sladorsoft/Intel8088OnBreadboard/schematics/part04/part04_1.kicad_sch

## KiCad design schematics/part04/part04_1.kicad_sch (2022-03-15)

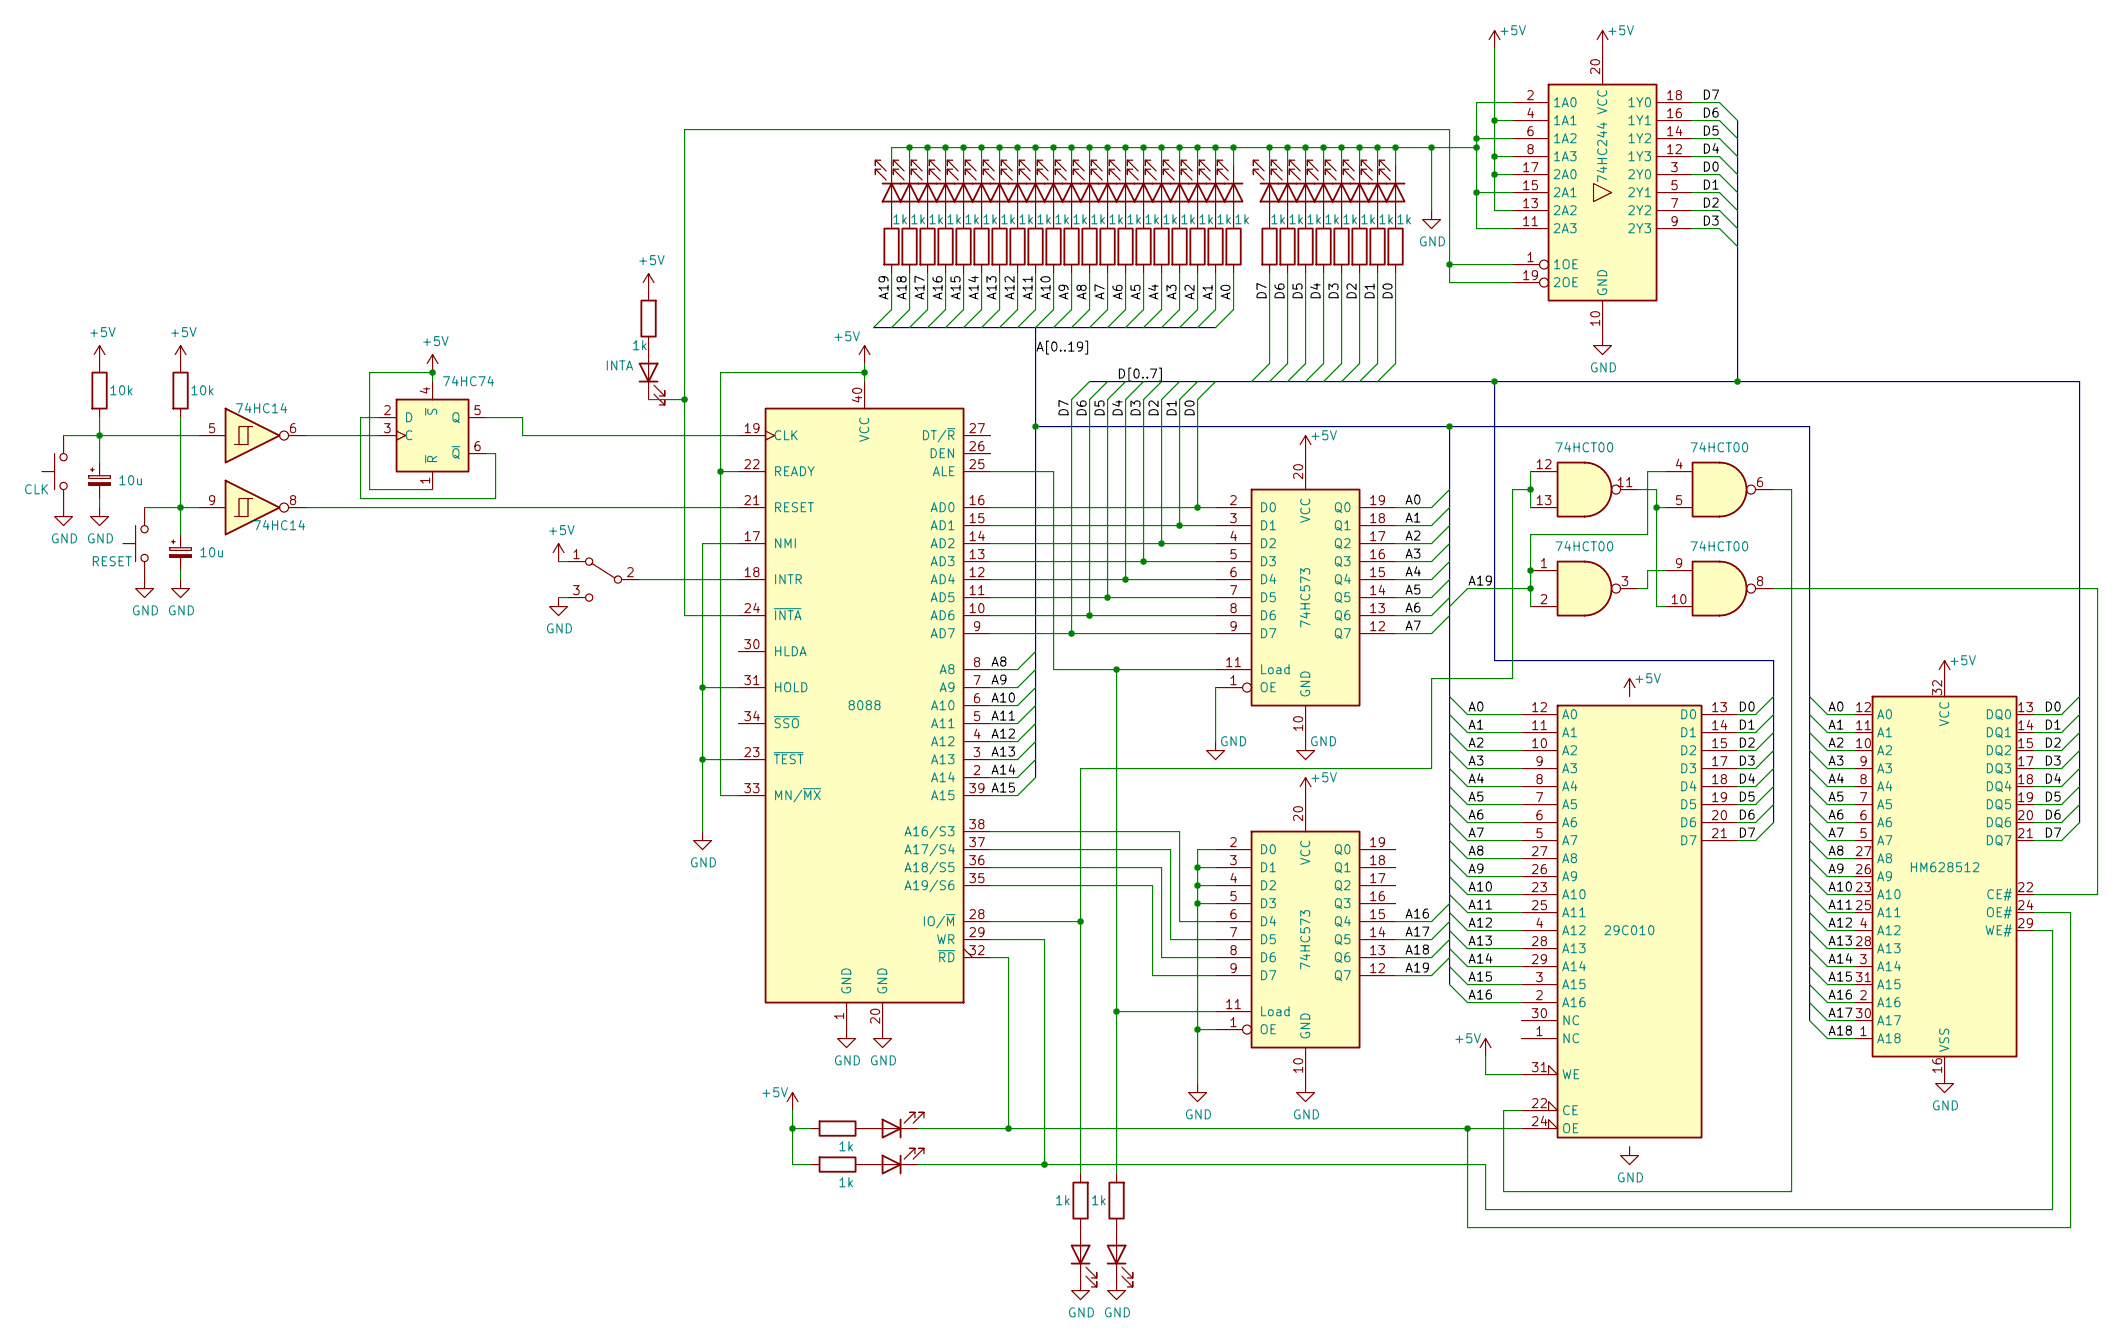
[picture p13: schematic part04_1.kicad_sch]

Parts:
SW1: INT
U1: 8088; DIP-40_W15.24mm
U2, U3: 74HC573
U4: 29C010
U5: 74HCT00
U6: HM628512; DIP-32_W15.24mm
U7: 74HC244
U101: 74HC74
U102: 74HC14

Connections:
+5V: U1.22 (READY), U1.33 (MN/~MX), U1.40 (VCC), U2.20 (VCC), U3.20 (VCC), U4.32 (VCC), U101.1 (~R), U101.4 (~S)
A0: U2.19 (Q0), U4.12 (A0), U6.12 (A0)
A1: U2.18 (Q1), U4.11 (A1), U6.11 (A1)
A2: U2.17 (Q2), U4.10 (A2), U6.10 (A2)
A3: U2.16 (Q3), U4.9 (A3), U6.9 (A3)
A4: U2.15 (Q4), U4.8 (A4), U6.8 (A4)
A5: U2.14 (Q5), U4.7 (A5), U6.7 (A5)
A6: U2.13 (Q6), U4.6 (A6), U6.6 (A6)
A7: U2.12 (Q7), U4.5 (A7), U6.5 (A7)
A8: U1.8 (A8), U4.27 (A8), U6.27 (A8)
A9: U1.7 (A9), U4.26 (A9), U6.26 (A9)
A10: U1.6 (A10), U4.23 (A10), U6.23 (A10)
A11: U1.5 (A11), U4.25 (A11), U6.25 (A11)
A12: U1.4 (A12), U4.4 (A12), U6.4 (A12)
A13: U1.3 (A13), U4.28 (A13), U6.28 (A13)
A14: U1.2 (A14), U4.29 (A14), U6.3 (A14)
A15: U1.39 (A15), U4.3 (A15), U6.31 (A15)
A16: U3.15 (Q4), U4.2 (A16), U6.2 (A16)
A17: U3.14 (Q5), U6.30 (A17)
A18: U3.13 (Q6), U6.1 (A18)
A19: U3.12 (Q7), U5.1, U5.2, U5.4
D0: U1.16 (AD0), U2.2 (D0), U4.13 (D0), U6.13 (DQ0), U7.3 (2Y0)
D1: U1.15 (AD1), U2.3 (D1), U4.14 (D1), U6.14 (DQ1), U7.5 (2Y1)
D2: U1.14 (AD2), U2.4 (D2), U4.15 (D2), U6.15 (DQ2), U7.7 (2Y2)
D3: U1.13 (AD3), U2.5 (D3), U4.17 (D3), U6.17 (DQ3), U7.9 (2Y3)
D4: U1.12 (AD4), U2.6 (D4), U4.18 (D4), U6.18 (DQ4), U7.12 (1Y3)
D5: U1.11 (AD5), U2.7 (D5), U4.19 (D5), U6.19 (DQ5), U7.14 (1Y2)
D6: U1.10 (AD6), U2.8 (D6), U4.20 (D6), U6.20 (DQ6), U7.16 (1Y1)
D7: U1.9 (AD7), U2.9 (D7), U4.21 (D7), U6.21 (DQ7), U7.18 (1Y0)
GND: U1.1 (GND), U1.17 (NMI), U1.20 (GND), U1.23 (~TEST), U1.31 (HOLD), U2.1 (OE), U2.10 (GND), U3.1 (OE), U3.2 (D0), U3.3 (D1), U3.4 (D2), U3.5 (D3), U3.10 (GND), U4.16 (GND), U7.2 (1A0), U7.6 (1A2), U7.11 (2A3), U7.15 (2A1)
unnamed: SW1.2 (B), U1.18 (INTR)
unnamed: U1.19 (CLK), U101.5 (Q)
unnamed: U1.21 (RESET), U102.8
unnamed: U1.24 (~INTA), U7.1 (1OE), U7.19 (2OE)
unnamed: U1.25 (ALE), U2.11 (Load), U3.11 (Load)
unnamed: U1.28 (IO/~M), U5.12, U5.13
unnamed: U1.29 (WR), U6.29 (WE#)
unnamed: U1.32 (~RD), U4.24 (OE), U6.24 (OE#)
unnamed: U1.35 (A19/S6), U3.9 (D7)
unnamed: U1.36 (A18/S5), U3.8 (D6)
unnamed: U1.37 (A17/S4), U3.7 (D5)
unnamed: U1.38 (A16/S3), U3.6 (D4)
unnamed: U4.22 (CE), U5.6
unnamed: U5.3, U5.9
unnamed: U5.8, U6.22 (CE#)
unnamed: U5.5, U5.10, U5.11
unnamed: U7.4 (1A1), U7.8 (1A3), U7.13 (2A2), U7.17 (2A0)
unnamed: U101.2 (D), U101.6 (~Q)
unnamed: U101.3 (C), U102.6
