sladorsoft/Intel8088OnBreadboard/schematics/part06/part06_1.kicad_sch

## KiCad design schematics/part06/part06_1.kicad_sch (2022-04-28)

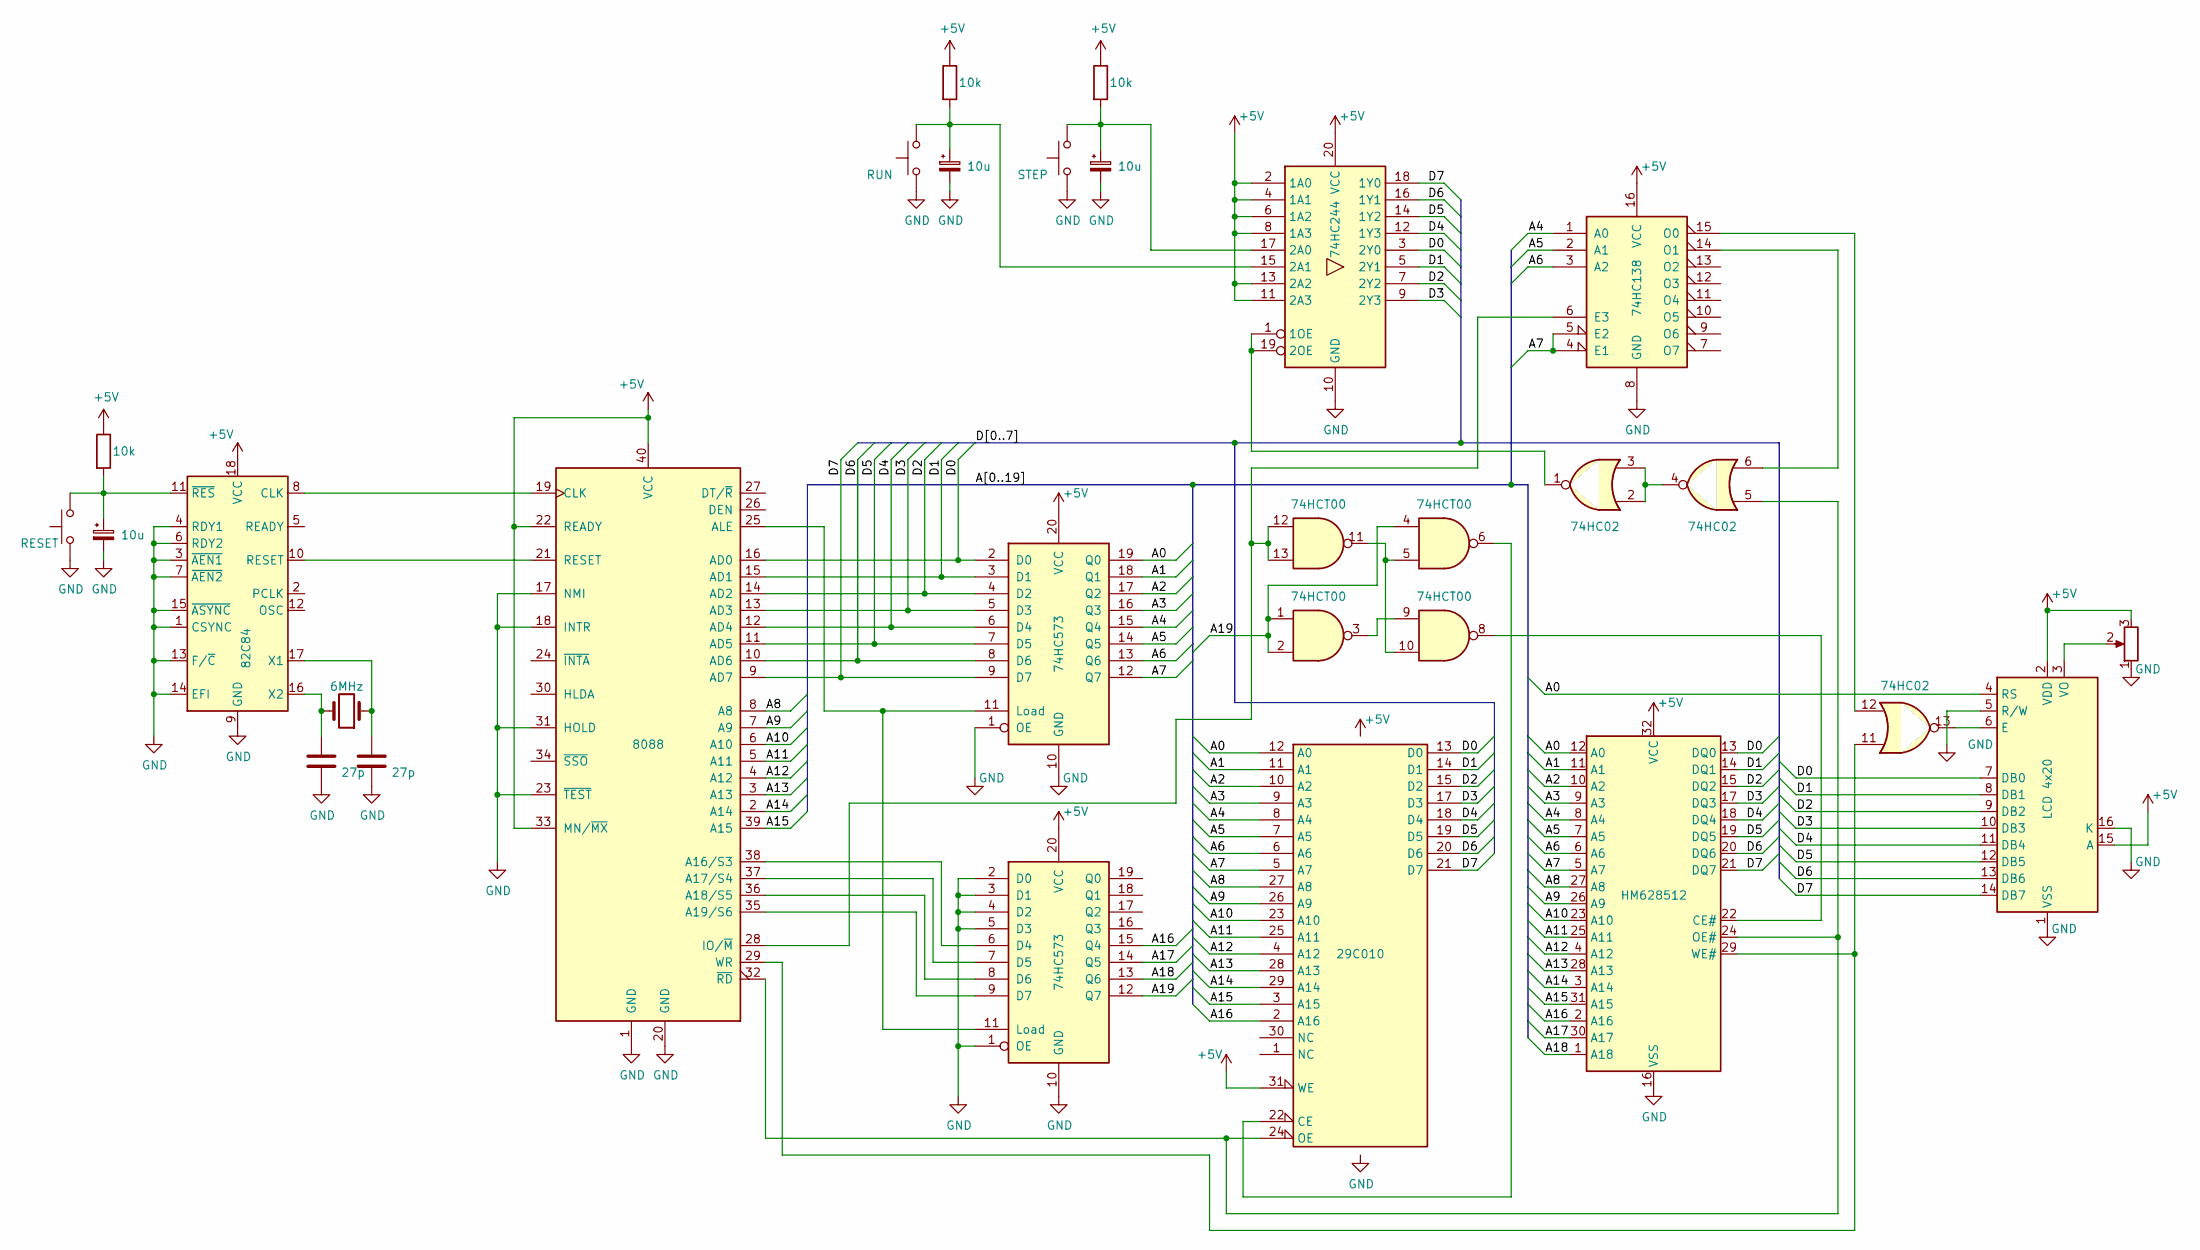
[picture p16: schematic part06_1.kicad_sch]

Parts:
C1, C4, C5: 10u
C2, C3: 27p
R1, R2, R3: 10k
RV1: R_Potentiometer
SW1: RESET
SW2: STEP
SW3: RUN
U1: 8088; DIP-40_W15.24mm
U2, U3: 74HC573
U4: 29C010
U5: 74HCT00
U6: HM628512; DIP-32_W15.24mm
U7: 74HC244
U8: 74HC138
U9: 74HC02
U10: LCD 4x20; NHD-0420H1Z
U11: 82C84; DIP-18_W7.62mm
Y1: 6MHz

Connections:
+5V: R1.1, R2.1, R3.1, RV1.3, U1.22 (READY), U1.33 (MN/~MX), U1.40 (VCC), U2.20 (VCC), U3.20 (VCC), U4.31 (PGM), U4.32 (VCC), U6.32 (VCC), U7.2 (1A0), U7.4 (1A1), U7.6 (1A2), U7.8 (1A3), U7.11 (2A3), U7.13 (2A2), U7.20 (VCC), U8.16 (VCC), U10.2 (VDD), U10.15 (A), U11.18 (VCC)
A0: U2.19 (Q0), U4.12 (A0), U6.12 (A0), U10.4 (RS)
A1: U2.18 (Q1), U4.11 (A1), U6.11 (A1)
A2: U2.17 (Q2), U4.10 (A2), U6.10 (A2)
A3: U2.16 (Q3), U4.9 (A3), U6.9 (A3)
A4: U2.15 (Q4), U4.8 (A4), U6.8 (A4), U8.1 (A0)
A5: U2.14 (Q5), U4.7 (A5), U6.7 (A5), U8.2 (A1)
A6: U2.13 (Q6), U4.6 (A6), U6.6 (A6), U8.3 (A2)
A7: U2.12 (Q7), U4.5 (A7), U6.5 (A7), U8.4 (E1), U8.5 (E2)
A8: U1.8 (A8), U4.27 (A8), U6.27 (A8)
A9: U1.7 (A9), U4.26 (A9), U6.26 (A9)
A10: U1.6 (A10), U4.23 (A10), U6.23 (A10)
A11: U1.5 (A11), U4.25 (A11), U6.25 (A11)
A12: U1.4 (A12), U4.4 (A12), U6.4 (A12)
A13: U1.3 (A13), U4.28 (A13), U6.28 (A13)
A14: U1.2 (A14), U4.29 (A14), U6.3 (A14)
A15: U1.39 (A15), U4.3 (A15), U6.31 (A15)
A16: U3.15 (Q4), U4.2 (A16), U6.2 (A16)
A17: U3.14 (Q5), U6.30 (A17)
A18: U3.13 (Q6), U6.1 (A18)
A19: U3.12 (Q7), U5.1, U5.2, U5.4
D0: U1.16 (AD0), U2.2 (D0), U4.13 (D0), U6.13 (DQ0), U7.3 (2Y0), U10.7 (DB0)
D1: U1.15 (AD1), U2.3 (D1), U4.14 (D1), U6.14 (DQ1), U7.5 (2Y1), U10.8 (DB1)
D2: U1.14 (AD2), U2.4 (D2), U4.15 (D2), U6.15 (DQ2), U7.7 (2Y2), U10.9 (DB2)
D3: U1.13 (AD3), U2.5 (D3), U4.17 (D3), U6.17 (DQ3), U7.9 (2Y3), U10.10 (DB3)
D4: U1.12 (AD4), U2.6 (D4), U4.18 (D4), U6.18 (DQ4), U7.12 (1Y3), U10.11 (DB4)
D5: U1.11 (AD5), U2.7 (D5), U4.19 (D5), U6.19 (DQ5), U7.14 (1Y2), U10.12 (DB5)
D6: U1.10 (AD6), U2.8 (D6), U4.20 (D6), U6.20 (DQ6), U7.16 (1Y1), U10.13 (DB6)
D7: U1.9 (AD7), U2.9 (D7), U4.21 (D7), U6.21 (DQ7), U7.18 (1Y0), U10.14 (DB7)
GND: C1.2, C2.2, C3.2, C4.2, C5.2, RV1.1, SW1.1, SW2.1, SW3.1, U1.1 (GND), U1.17 (NMI), U1.18 (INTR), U1.20 (GND), U1.23 (~TEST), U1.31 (HOLD), U2.1 (OE), U2.10 (GND), U3.1 (OE), U3.2 (D0), U3.3 (D1), U3.4 (D2), U3.5 (D3), U3.10 (GND), U4.16 (GND), U6.16 (VSS), U7.10 (GND), U8.8 (GND), U10.1 (VSS), U10.5 (R/W), U10.16 (K), U11.1 (CSYNC), U11.3 (~AEN1), U11.4 (RDY1), U11.6 (RDY2), U11.7 (~AEN2), U11.9 (GND), U11.13 (F/~C), U11.14 (EFI), U11.15 (~ASYNC)
unnamed: C1.1, R1.2, SW1.2, U11.11 (~RES)
unnamed: C2.1, U11.16 (X2), Y1.2
unnamed: C3.1, U11.17 (X1), Y1.1
unnamed: C4.1, R2.2, SW2.2, U7.17 (2A0)
unnamed: C5.1, R3.2, SW3.2, U7.15 (2A1)
unnamed: RV1.2, U10.3 (VO)
unnamed: U1.19 (CLK), U11.8 (CLK)
unnamed: U1.21 (RESET), U11.10 (RESET)
unnamed: U1.25 (ALE), U2.11 (Load), U3.11 (Load)
unnamed: U1.28 (IO/~M), U5.12, U5.13, U8.6 (E3)
unnamed: U1.29 (WR), U6.29 (WE#), U9.11
unnamed: U1.32 (~RD), U4.24 (OE), U6.24 (OE#), U9.5
unnamed: U1.35 (A19/S6), U3.9 (D7)
unnamed: U1.36 (A18/S5), U3.8 (D6)
unnamed: U1.37 (A17/S4), U3.7 (D5)
unnamed: U1.38 (A16/S3), U3.6 (D4)
unnamed: U4.22 (CE), U5.6
unnamed: U5.3, U5.9
unnamed: U5.8, U6.22 (CE#)
unnamed: U5.5, U5.10, U5.11
unnamed: U7.1 (1OE), U7.19 (2OE), U9.1
unnamed: U8.14 (O1), U9.6
unnamed: U8.15 (O0), U9.12
unnamed: U9.2, U9.3, U9.4
unnamed: U9.13, U10.6 (E)
