sladorsoft/Intel8088OnBreadboard/schematics/part08/part08.kicad_sch

## KiCad design schematics/part08/part08.kicad_sch (2023-01-09)

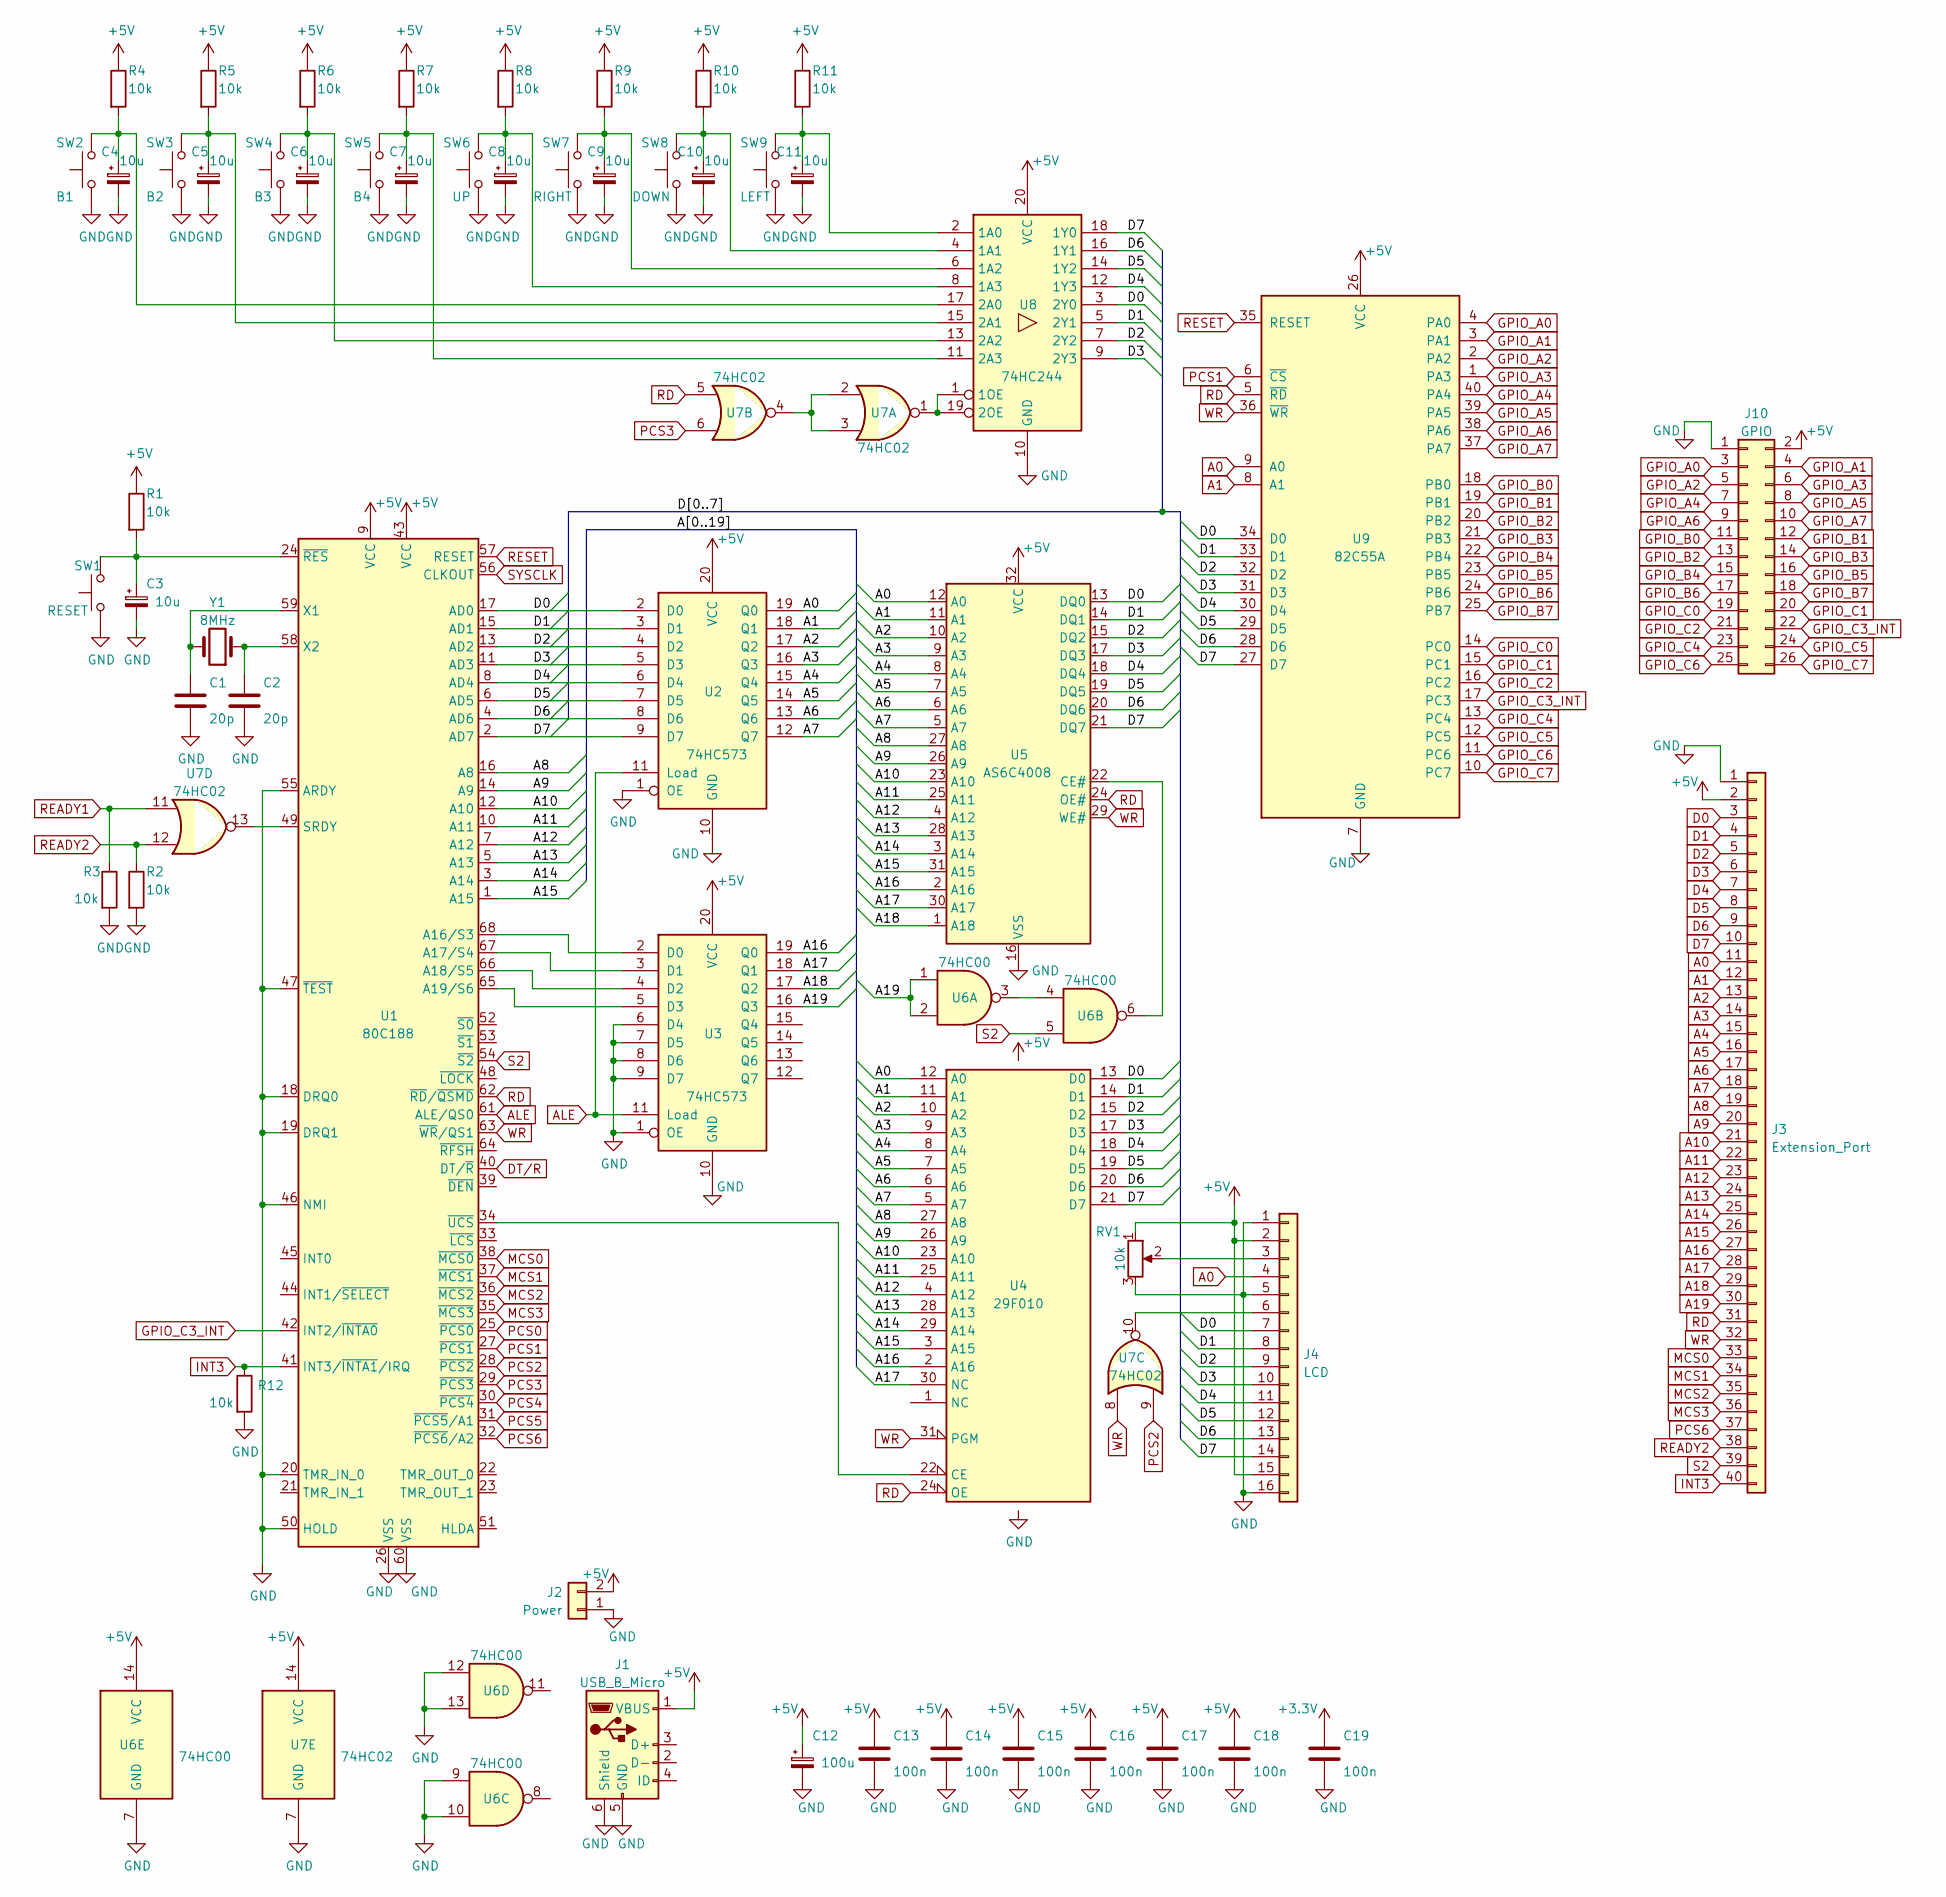
[picture p18: schematic part08.kicad_sch]

Parts:
C1, C2: 20p; C_Rect_L7.0mm_W3.5mm_P5.00mm
C3, C4, C5, C6, C7, C8, C9, C10, C11: 10u; CP_Radial_D5.0mm_P2.50mm
C12: 100u; CP_Radial_D5.0mm_P2.50mm
C13, C14, C15, C16, C17, C18, C19: 100n; C_Rect_L7.0mm_W3.5mm_P5.00mm
J1: USB_B_Micro; USB_Micro-B_Molex-105017-0001
J2: Power; JST_XH_B2B-XH-AM_1x02_P2.50mm_Vertical
J3: Extension_Port; PinHeader_1x40_P2.54mm_Vertical
J4: LCD; PinHeader_1x16_P2.54mm_Vertical
J10: GPIO; PinHeader_2x13_P2.54mm_Vertical
R1, R2, R3, R4, R5, R6, R7, R8, R9, R10, R11, R12: 10k; R_Axial_DIN0207_L6.3mm_D2.5mm_P10.16mm_Horizontal
RV1: 10k; Potentiometer_ACP_CA14-H4_Horizontal
SW1: RESET; SW_PUSH_6mm_H5mm
SW2: B1; SW_PUSH_6mm_H5mm
SW3: B2; SW_PUSH_6mm_H5mm
SW4: B3; SW_PUSH_6mm_H5mm
SW5: B4; SW_PUSH_6mm_H5mm
SW6: UP; SW_PUSH_6mm_H5mm
SW7: RIGHT; SW_PUSH_6mm_H5mm
SW8: DOWN; SW_PUSH_6mm_H5mm
SW9: LEFT; SW_PUSH_6mm_H5mm
U1: 80C188; PLCC-68_THT-Corner-Socket
U2, U3: 74HC573; DIP-20_W7.62mm_Socket
U4: 29F010; DIP-32_W15.24mm_Socket
U5: AS6C4008; DIP-32_W15.24mm_Socket
U6: 74HC00; DIP-14_W7.62mm_Socket
U7: 74HC02; DIP-14_W7.62mm_Socket
U8: 74HC244; DIP-20_W7.62mm_Socket
U9: 82C55A; DIP-40_W15.24mm_Socket
Y1: 8MHz; Crystal_HC18-U_Vertical

Connections:
+3.3V: C19.1
+5V: C12.1, C13.1, C14.1, C15.1, C16.1, C17.1, C18.1, J1.1 (VBUS), J2.2, J3.2, J4.2, J4.15, J10.2, R1.1, R4.1, R5.1, R6.1, R7.1, R8.1, R9.1, R10.1, R11.1, RV1.1, U1.9 (VCC), U1.43 (VCC), U2.20 (VCC), U3.20 (VCC), U4.32 (VCC), U5.32 (VCC), U6.14 (VCC), U7.14 (VCC), U8.20 (VCC), U9.26 (VCC)
A0: J3.11, J4.4, U2.19 (Q0), U4.12 (A0), U5.12 (A0), U9.9 (A0)
A1: J3.12, U2.18 (Q1), U4.11 (A1), U5.11 (A1), U9.8 (A1)
A2: J3.13, U2.17 (Q2), U4.10 (A2), U5.10 (A2)
A3: J3.14, U2.16 (Q3), U4.9 (A3), U5.9 (A3)
A4: J3.15, U2.15 (Q4), U4.8 (A4), U5.8 (A4)
A5: J3.16, U2.14 (Q5), U4.7 (A5), U5.7 (A5)
A6: J3.17, U2.13 (Q6), U4.6 (A6), U5.6 (A6)
A7: J3.18, U2.12 (Q7), U4.5 (A7), U5.5 (A7)
A8: J3.19, U1.16 (A8), U4.27 (A8), U5.27 (A8)
A9: J3.20, U1.14 (A9), U4.26 (A9), U5.26 (A9)
A10: J3.21, U1.12 (A10), U4.23 (A10), U5.23 (A10)
A11: J3.22, U1.10 (A11), U4.25 (A11), U5.25 (A11)
A12: J3.23, U1.7 (A12), U4.4 (A12), U5.4 (A12)
A13: J3.24, U1.5 (A13), U4.28 (A13), U5.28 (A13)
A14: J3.25, U1.3 (A14), U4.29 (A14), U5.3 (A14)
A15: J3.26, U1.1 (A15), U4.3 (A15), U5.31 (A15)
A16: J3.27, U3.19 (Q0), U4.2 (A16), U5.2 (A16)
A17: J3.28, U3.18 (Q1), U4.30 (NC), U5.30 (A17)
A18: J3.29, U3.17 (Q2), U5.1 (A18)
A19: J3.30, U3.16 (Q3), U6.1, U6.2
ALE: U1.61 (ALE/QS0), U2.11 (Load), U3.11 (Load)
D0: J3.3, J4.7, U1.17 (AD0), U2.2 (D0), U4.13 (D0), U5.13 (DQ0), U8.3 (2Y0), U9.34 (D0)
D1: J3.4, J4.8, U1.15 (AD1), U2.3 (D1), U4.14 (D1), U5.14 (DQ1), U8.5 (2Y1), U9.33 (D1)
D2: J3.5, J4.9, U1.13 (AD2), U2.4 (D2), U4.15 (D2), U5.15 (DQ2), U8.7 (2Y2), U9.32 (D2)
D3: J3.6, J4.10, U1.11 (AD3), U2.5 (D3), U4.17 (D3), U5.17 (DQ3), U8.9 (2Y3), U9.31 (D3)
D4: J3.7, J4.11, U1.8 (AD4), U2.6 (D4), U4.18 (D4), U5.18 (DQ4), U8.12 (1Y3), U9.30 (D4)
D5: J3.8, J4.12, U1.6 (AD5), U2.7 (D5), U4.19 (D5), U5.19 (DQ5), U8.14 (1Y2), U9.29 (D5)
D6: J3.9, J4.13, U1.4 (AD6), U2.8 (D6), U4.20 (D6), U5.20 (DQ6), U8.16 (1Y1), U9.28 (D6)
D7: J3.10, J4.14, U1.2 (AD7), U2.9 (D7), U4.21 (D7), U5.21 (DQ7), U8.18 (1Y0), U9.27 (D7)
DT/R: U1.40 (DT/~R)
GND: C1.2, C2.2, C3.2, C4.2, C5.2, C6.2, C7.2, C8.2, C9.2, C10.2, C11.2, C12.2, C13.2, C14.2, C15.2, C16.2, C17.2, C18.2, C19.2, J1.5 (GND), J1.6 (Shield), J2.1, J3.1, J4.1, J4.5, J4.16, J10.1, R2.2, R3.2, R12.2, RV1.3, SW1.1, SW2.1, SW3.1, SW4.1, SW5.1, SW6.1, SW7.1, SW8.1, SW9.1, U1.18 (DRQ0), U1.19 (DRQ1), U1.20 (TMR_IN_0), U1.26 (VSS), U1.46 (NMI), U1.47 (~TEST), U1.50 (HOLD), U1.55 (ARDY), U1.60 (VSS), U2.1 (OE), U2.10 (GND), U3.1 (OE), U3.6 (D4), U3.7 (D5), U3.8 (D6), U3.9 (D7), U3.10 (GND), U4.16 (GND), U5.16 (VSS), U6.7 (GND), U6.9, U6.10, U6.12, U6.13, U7.7 (GND), U8.10 (GND), U9.7 (GND)
GPIO_A0: J10.3, U9.4 (PA0)
GPIO_A1: J10.4, U9.3 (PA1)
GPIO_A2: J10.5, U9.2 (PA2)
GPIO_A3: J10.6, U9.1 (PA3)
GPIO_A4: J10.7, U9.40 (PA4)
GPIO_A5: J10.8, U9.39 (PA5)
GPIO_A6: J10.9, U9.38 (PA6)
GPIO_A7: J10.10, U9.37 (PA7)
GPIO_B0: J10.11, U9.18 (PB0)
GPIO_B1: J10.12, U9.19 (PB1)
GPIO_B2: J10.13, U9.20 (PB2)
GPIO_B3: J10.14, U9.21 (PB3)
GPIO_B4: J10.15, U9.22 (PB4)
GPIO_B5: J10.16, U9.23 (PB5)
GPIO_B6: J10.17, U9.24 (PB6)
GPIO_B7: J10.18, U9.25 (PB7)
GPIO_C0: J10.19, U9.14 (PC0)
GPIO_C1: J10.20, U9.15 (PC1)
GPIO_C2: J10.21, U9.16 (PC2)
GPIO_C3_INT: J10.22, U1.42 (INT2/~INTA0), U9.17 (PC3)
GPIO_C4: J10.23, U9.13 (PC4)
GPIO_C5: J10.24, U9.12 (PC5)
GPIO_C6: J10.25, U9.11 (PC6)
GPIO_C7: J10.26, U9.10 (PC7)
INT3: J3.40, R12.1, U1.41 (INT3/~INTA1/IRQ)
MCS0: J3.33, U1.38 (~MCS0)
MCS1: J3.34, U1.37 (~MCS1)
MCS2: J3.35, U1.36 (~MCS2)
MCS3: J3.36, U1.35 (~MCS3)
unnamed: C1.1, U1.59 (X1), Y1.2
unnamed: C2.1, U1.58 (X2), Y1.1
unnamed: C3.1, R1.2, SW1.2, U1.24 (~RES)
unnamed: C4.1, R4.2, SW2.2, U8.17 (2A0)
unnamed: C5.1, R5.2, SW3.2, U8.15 (2A1)
unnamed: C6.1, R6.2, SW4.2, U8.13 (2A2)
unnamed: C7.1, R7.2, SW5.2, U8.11 (2A3)
unnamed: C8.1, R8.2, SW6.2, U8.8 (1A3)
unnamed: C9.1, R9.2, SW7.2, U8.6 (1A2)
unnamed: C10.1, R10.2, SW8.2, U8.4 (1A1)
unnamed: C11.1, R11.2, SW9.2, U8.2 (1A0)
unnamed: J4.3, RV1.2
unnamed: J4.6, U7.10
unnamed: U1.34 (~UCS), U4.22 (CE)
unnamed: U1.49 (SRDY), U7.13
unnamed: U1.65 (A19/S6), U3.5 (D3)
unnamed: U1.66 (A18/S5), U3.4 (D2)
unnamed: U1.67 (A17/S4), U3.3 (D1)
unnamed: U1.68 (A16/S3), U3.2 (D0)
unnamed: U5.22 (CE#), U6.6
unnamed: U6.3, U6.4
unnamed: U7.1, U8.1 (1OE), U8.19 (2OE)
unnamed: U7.2, U7.3, U7.4
PCS0: U1.25 (~PCS0)
PCS1: U1.27 (~PCS1), U9.6 (~CS)
PCS2: U1.28 (~PCS2), U7.9
PCS3: U1.29 (~PCS3), U7.6
PCS4: U1.30 (~PCS4)
PCS5: U1.31 (~PCS5/A1)
PCS6: J3.37, U1.32 (~PCS6/A2)
RD: J3.31, U1.62 (~RD/~QSMD), U4.24 (OE), U5.24 (OE#), U7.5, U9.5 (~RD)
READY1: R3.1, U7.11
READY2: J3.38, R2.1, U7.12
RESET: U1.57 (RESET), U9.35 (RESET)
S2: J3.39, U1.54 (~S2), U6.5
SYSCLK: U1.56 (CLKOUT)
WR: J3.32, U1.63 (~WR/QS1), U4.31 (PGM), U5.29 (WE#), U7.8, U9.36 (~WR)
